mlduff/camtrap/device/client/main/camera/camera.c

/*
 * SPDX-FileCopyrightText: 2010-2022 Espressif Systems (Shanghai) CO LTD
 *
 * SPDX-License-Identifier: CC0-1.0
 */

#include <esp_log.h>

#define CAMERA_MODEL_WROVER_KIT

#include "camera_pins.h"
#include "camera.h"

static const char *TAG = "client:camera";

esp_err_t camera_capture(capture_func func)
{
    // acquire a frame
    camera_fb_t *fb = esp_camera_fb_get();
    if (!fb)
    {
        ESP_LOGE(TAG, "Camera capture failed");
        return ESP_FAIL;
    }

    ESP_LOGI(TAG, "Camera capture succeeded.");
    func(fb);

    // return the frame buffer back to the driver for reuse
    esp_camera_fb_return(fb);
    return ESP_OK;
}

/**
 * Initialize the camera.
 */
esp_err_t camera_init()
{
    camera_config_t config;
    config.ledc_channel = LEDC_CHANNEL_0;
    config.ledc_timer = LEDC_TIMER_0;
    config.pin_d0 = Y2_GPIO_NUM;
    config.pin_d1 = Y3_GPIO_NUM;
    config.pin_d2 = Y4_GPIO_NUM;
    config.pin_d3 = Y5_GPIO_NUM;
    config.pin_d4 = Y6_GPIO_NUM;
    config.pin_d5 = Y7_GPIO_NUM;
    config.pin_d6 = Y8_GPIO_NUM;
    config.pin_d7 = Y9_GPIO_NUM;
    config.pin_xclk = XCLK_GPIO_NUM;
    config.pin_pclk = PCLK_GPIO_NUM;
    config.pin_vsync = VSYNC_GPIO_NUM;
    config.pin_href = HREF_GPIO_NUM;
    config.pin_sccb_sda = SIOD_GPIO_NUM;
    config.pin_sccb_scl = SIOC_GPIO_NUM;
    config.pin_pwdn = PWDN_GPIO_NUM;
    config.pin_reset = RESET_GPIO_NUM;
    config.xclk_freq_hz = 20000000;
    config.frame_size = FRAMESIZE_UXGA;
    config.pixel_format = PIXFORMAT_JPEG;
    config.grab_mode = CAMERA_GRAB_LATEST;
    config.fb_location = CAMERA_FB_IN_PSRAM;
    config.jpeg_quality = 12;
    config.fb_count = 2; // Must be more than one for CAMERA_GRAB_LATEST to work properly

    return esp_camera_init(&config);
}
