mlduff/camtrap/device/client/main/storage/spiffs.c

#include "esp_spiffs.h"

void init_spiffs() {
    esp_vfs_spiffs_conf_t conf = {
        .base_path = "/spiffs",
        .partition_label = NULL,
        .max_files = 1,
        .format_if_mount_failed = true
    };

    esp_err_t ret = esp_vfs_spiffs_register(&conf);

    if (ret != ESP_OK) {
        if (ret == ESP_FAIL) {
            printf("Failed to mount or format filesystem\n");
        } else if (ret == ESP_ERR_NOT_FOUND) {
            printf("Failed to find SPIFFS partition\n");
        } else {
            printf("Failed to initialize SPIFFS (%s)\n", esp_err_to_name(ret));
        }
        return;
    }

    size_t total = 0, used = 0;
    ret = esp_spiffs_info(NULL, &total, &used);
    if (ret != ESP_OK) {
        printf("Failed to get SPIFFS partition information (%s)\n", esp_err_to_name(ret));
    } else {
        printf("Partition size: total: %d, used: %d\n", total, used);
    }
}
